SolarEnergyRacers/solar_car_control_system_v6/lib_common/CAN/CANBus.cpp

//
// CAN Bus
//
#include <Arduino.h>
#include <CANBus.h>
#include <CarState.h>
#include <Console.h>
#include <Helper.h>
#include <I2CBus.h>
#include <System.h>
#include <driver/twai.h>
#include <esp_err.h>
#include <esp_intr_alloc.h>
#include <fmt/core.h>
#include <freertos/FreeRTOS.h>
#include <freertos/semphr.h>
#include <global_definitions.h>

extern CarState carState;
extern Console console;
extern I2CBus i2cBus;
extern CANBus canBus;
extern bool SystemInited;

using namespace std;

constexpr uint16_t CANBus::MAX_RX_PACKETS_PER_CYCLE;
constexpr uint16_t CANBus::MAX_TX_PACKETS_PER_CYCLE;
constexpr uint16_t CANBus::TX_PRIORITY_SCAN_WINDOW;
constexpr uint16_t CANBus::REINIT_FAIL_THRESHOLD;
constexpr uint32_t CANBus::REINIT_COOLDOWN_MS;

static inline bool is_relevant_can_id(uint16_t packetId) {
    if (packetId == (AC_BASE_ADDR | 0x00) ||
        packetId == (DC_BASE_ADDR | 0x00) || packetId == (DC_BASE_ADDR | 0x01)) {
        return true;
    }

    if (packetId == BMS_BASE_ADDR ||
        packetId == (BMS_BASE_ADDR | 0xF7) ||
        packetId == (BMS_BASE_ADDR | 0xF8) ||
        packetId == (BMS_BASE_ADDR | 0xF9) ||
        packetId == (BMS_BASE_ADDR | 0xFA) ||
        packetId == (BMS_BASE_ADDR | 0xFD)) {
        return true;
    }

    if (packetId == (MPPT1_BASE_ADDR | 0x01) || packetId == (MPPT1_BASE_ADDR | 0x02) ||
        packetId == (MPPT2_BASE_ADDR | 0x01) || packetId == (MPPT2_BASE_ADDR | 0x02) ||
        packetId == (MPPT3_BASE_ADDR | 0x01) || packetId == (MPPT3_BASE_ADDR | 0x02) ||
        packetId == (MPPT4_BASE_ADDR | 0x01) || packetId == (MPPT4_BASE_ADDR | 0x02)) {
        return true;
    }

    return false;
}

static inline bool is_critical_can_tx_id(uint16_t packetId) {
    // Only the 0x661 packet carries a dedicated sequence byte in data byte 5.
    // The 0x650/0x660 life-sign packets use the first 16 bits as a heartbeat
    // value, so they should not trigger sequence-gap warnings.
    return packetId == (DC_BASE_ADDR | 0x01);
}

static bool extract_critical_sequence(uint16_t packetId, CANPacket& packet,
                                      uint16_t& sequence, uint8_t& bitWidth) {
    switch (packetId) {
        case (DC_BASE_ADDR | 0x01):
            sequence = packet.getData_u8(5);
            bitWidth = 8;
            return true;
        default:
            return false;
    }
}

static bool read_can_packet(CANPacket& outPacket) {
    twai_message_t message = {};
    esp_err_t err = twai_receive(&message, 0);
    if (err != ESP_OK) {
        return false;
    }

    if (message.extd || message.rtr || message.data_length_code > 8) {
        return false;
    }

    uint16_t packetId = static_cast<uint16_t>(message.identifier & 0x7FF);

    if (canBus.verboseModeCanAddr) {
        string indent = "";
        if ((packetId & 0xFF0) == 0x500) indent = "";
        if ((packetId & 0xFF0) == 0x600) indent = "      ";
        if ((packetId & 0xFF0) == 0x610) indent = "            ";
        if ((packetId & 0xFF0) == 0x620) indent = "                  ";
        if ((packetId & 0xFF0) == 0x630) indent = "                        ";
        if ((packetId & 0xFF0) == 0x650) indent = "                              ";
        if ((packetId & 0xFF0) == 0x660) indent = "                                    ";
        if ((packetId & 0xF00) == 0x700) indent = "                                          ";
        console << fmt::format("CAN packet ID:{}0x{:03X}", indent, packetId) << NL;
    }
    if (!is_relevant_can_id(packetId)) {
        return false;
    }

    uint64_t rxData = 0UL;
    for (uint8_t i = 0; i < message.data_length_code; i++) {
        rxData |= (static_cast<uint64_t>(message.data[i]) << (i * 8));
    }

    outPacket = CANPacket(packetId, rxData);
    return true;
}

bool CANBus::isPacketToRenew(uint16_t packetId) {
    auto maxAgeIt = max_ages.find(packetId);
    if (maxAgeIt == max_ages.end()) {
        return false;
    }

    int32_t maxAge = maxAgeIt->second;
    if (maxAge == -1) {
        return false;
    }
    if (maxAge == 0) {
        return true;
    }

    auto ageIt = ages.find(packetId);
    if (ageIt == ages.end() || ageIt->second == INT32_MAX) {
        return true;
    }

    return millis() - ageIt->second > maxAge;
}

void CANBus::setPacketTimeStamp(uint16_t packetId, int32_t millis) {
    auto ageIt = ages.find(packetId);
    if (ageIt != ages.end()) {
        ageIt->second = millis;
    }
}

CANBus::CANBus() { init_ages(); }

string CANBus::re_init() {
    lastReinitMs = millis();
    twai_stop();
    twai_driver_uninstall();
    vTaskDelay(50 / portTICK_PERIOD_MS);
    while (rxBufferOutCritical != nullptr && rxBufferOutCritical->isAvailable()) {
        rxBufferOutCritical->pop();
    }
    while (rxBufferOut.isAvailable()) {
        rxBufferOut.pop();
    }
    while (rxBufferIn.isAvailable()) {
        rxBufferIn.pop();
    }
    return CANBus::init();
}

string CANBus::init() {
    bool hasError = false;
    counterI = 0;
    counterR = 0;
    counterW = 0;
    counterI_notAvail = 0;
    counterR_notAvail = 0;
    counterW_notAvail = 0;
    counterRxOverwrite = 0;
    counterTxOverwrite = 0;
    counterCriticalTxDrop = 0;
    counterCriticalTxFail = 0;
    counterCriticalStale = 0;
    counterCriticalSeqGap = 0;
    criticalTxRetries.clear();
    criticalStaleActive.clear();
    criticalLastSeq.clear();
    criticalSeqSeen.clear();
    txFailStreak = 0;

    counterMaxPacketsIn = 0;
    counterMaxPacketsOut = 0;

    mutex_out = xSemaphoreCreateBinary();
    xSemaphoreGive(mutex_out);

    if (rxBufferOutCritical == nullptr) {
        rxBufferOutCritical = new CANRxBuffer();
    }
    if (rxBufferOutCritical == nullptr) {
        hasError = true;
        console << "     ERROR: Critical CAN queue allocation failed. Falling back to shared TX queue.\n";
    }

    twai_general_config_t g_config = TWAI_GENERAL_CONFIG_DEFAULT(
        static_cast<gpio_num_t>(CAN_TX), static_cast<gpio_num_t>(CAN_RX), TWAI_MODE_NORMAL);
    g_config.tx_queue_len = 64;
    g_config.rx_queue_len = 64;
    // Use a shared low/medium priority interrupt to reduce allocation failures
    // on systems with many peripherals already reserving dedicated interrupt lines.
    g_config.intr_flags = ESP_INTR_FLAG_LOWMED | ESP_INTR_FLAG_SHARED;
    g_config.alerts_enabled = TWAI_ALERT_TX_FAILED | TWAI_ALERT_BUS_OFF |
                              TWAI_ALERT_BUS_RECOVERED | TWAI_ALERT_ERR_PASS;

    twai_timing_config_t t_config = TWAI_TIMING_CONFIG_125KBITS();
    twai_filter_config_t f_config = TWAI_FILTER_CONFIG_ACCEPT_ALL();

    esp_err_t installErr = twai_driver_install(&g_config, &t_config, &f_config);
    esp_err_t startErr = installErr == ESP_OK ? twai_start() : installErr;

    if (installErr != ESP_OK || startErr != ESP_OK) {
        hasError = true;
        console << fmt::format(
            "     ERROR: TWAI init failed with rx={}, tx={}, speed={} (install={}, start={}).\n",
            CAN_RX, CAN_TX, CAN_SPEED, static_cast<int>(installErr), static_cast<int>(startErr));
    } else {
        console << fmt::format("     TWAI with rx={}, tx={}, speed={} inited.\n",
                               CAN_RX, CAN_TX, CAN_SPEED);
    }
    return fmt::format("[{}] CANBus initialized.", hasError ? "--" : "ok");
}

void CANBus::exit() {
    twai_stop();
    twai_driver_uninstall();
}

void CANBus::init_ages() {
    max_ages[AC_BASE_ADDR | 0x00] = CRITICAL_CAN_STALE_TIMEOUT_MS;
    max_ages[DC_BASE_ADDR | 0x00] = CRITICAL_CAN_STALE_TIMEOUT_MS;
    max_ages[DC_BASE_ADDR | 0x01] = CRITICAL_CAN_STALE_TIMEOUT_MS;

    // init max ages
    max_ages[BMS_BASE_ADDR] = MAXAGE_BMU_HEARTBEAT;
    max_ages[BMS_BASE_ADDR | 0x1] = MAXAGE_CMU_TEMP;      // CMU1
    max_ages[BMS_BASE_ADDR | 0x2] = MAXAGE_CMU_VOLTAGES;  // CMU1
    max_ages[BMS_BASE_ADDR | 0x3] = MAXAGE_CMU_VOLTAGES;  // CMU1
    max_ages[BMS_BASE_ADDR | 0x4] = MAXAGE_CMU_TEMP;      // CMU2
    max_ages[BMS_BASE_ADDR | 0x5] = MAXAGE_CMU_VOLTAGES;  // CMU2
    max_ages[BMS_BASE_ADDR | 0x6] = MAXAGE_CMU_VOLTAGES;  // CMU2
    max_ages[BMS_BASE_ADDR | 0x7] = MAXAGE_CMU_TEMP;      // CMU3
    max_ages[BMS_BASE_ADDR | 0x8] = MAXAGE_CMU_VOLTAGES;  // CMU3
    max_ages[BMS_BASE_ADDR | 0x9] = MAXAGE_CMU_VOLTAGES;  // CMU3
    max_ages[BMS_BASE_ADDR | 0xF4] = MAXAGE_PACK_SOC;
    max_ages[BMS_BASE_ADDR | 0xF5] = MAXAGE_BALANCE_SOC;
    max_ages[BMS_BASE_ADDR | 0xF6] = MAXAGE_CHARGER_CONTROL;
    max_ages[BMS_BASE_ADDR | 0xF7] = MAXAGE_PRECHARGE_STATUS;
    max_ages[BMS_BASE_ADDR | 0xF8] = MAXAGE_MIN_MAX_U_CELL;
    max_ages[BMS_BASE_ADDR | 0xF9] = MAXAGE_MIN_MAX_T_CELL;
    max_ages[BMS_BASE_ADDR | 0xFA] = MAXAGE_PACK_VOLTAGE;
    max_ages[BMS_BASE_ADDR | 0xFB] = MAXAGE_PACK_STATUS;
    max_ages[BMS_BASE_ADDR | 0xFC] = MAXAGE_PACK_FAN_STATUS;
    max_ages[BMS_BASE_ADDR | 0xFD] = MAXAGE_EXT_PACK_STATUS;

    max_ages[MPPT1_BASE_ADDR] = MAXAGE_MPPT_INPUT;
    max_ages[MPPT1_BASE_ADDR | 0x1] = MAXAGE_MPPT_OUTPUT;
    max_ages[MPPT1_BASE_ADDR | 0x2] = MAXAGE_MPPT_TEMP;
    max_ages[MPPT1_BASE_ADDR | 0x3] = MAXAGE_MPPT_AUX_POWER;
    max_ages[MPPT1_BASE_ADDR | 0x4] = MAXAGE_MPPT_LIMITS;
    max_ages[MPPT1_BASE_ADDR | 0x5] = MAXAGE_MPPT_STATUS;
    max_ages[MPPT1_BASE_ADDR | 0x6] = MAXAGE_MPPT_POWER_CONN;

    max_ages[MPPT2_BASE_ADDR] = MAXAGE_MPPT_INPUT;
    max_ages[MPPT2_BASE_ADDR | 0x1] = MAXAGE_MPPT_OUTPUT;
    max_ages[MPPT2_BASE_ADDR | 0x2] = MAXAGE_MPPT_TEMP;
    max_ages[MPPT2_BASE_ADDR | 0x3] = MAXAGE_MPPT_AUX_POWER;
    max_ages[MPPT2_BASE_ADDR | 0x4] = MAXAGE_MPPT_LIMITS;
    max_ages[MPPT2_BASE_ADDR | 0x5] = MAXAGE_MPPT_STATUS;
    max_ages[MPPT2_BASE_ADDR | 0x6] = MAXAGE_MPPT_POWER_CONN;

    max_ages[MPPT3_BASE_ADDR] = MAXAGE_MPPT_INPUT;
    max_ages[MPPT3_BASE_ADDR | 0x1] = MAXAGE_MPPT_OUTPUT;
    max_ages[MPPT3_BASE_ADDR | 0x2] = MAXAGE_MPPT_TEMP;
    max_ages[MPPT3_BASE_ADDR | 0x3] = MAXAGE_MPPT_AUX_POWER;
    max_ages[MPPT3_BASE_ADDR | 0x4] = MAXAGE_MPPT_LIMITS;
    max_ages[MPPT3_BASE_ADDR | 0x5] = MAXAGE_MPPT_STATUS;
    max_ages[MPPT3_BASE_ADDR | 0x6] = MAXAGE_MPPT_POWER_CONN;

    max_ages[MPPT4_BASE_ADDR] = MAXAGE_MPPT_INPUT;
    max_ages[MPPT4_BASE_ADDR | 0x1] = MAXAGE_MPPT_OUTPUT;
    max_ages[MPPT4_BASE_ADDR | 0x2] = MAXAGE_MPPT_TEMP;
    max_ages[MPPT4_BASE_ADDR | 0x3] = MAXAGE_MPPT_AUX_POWER;
    max_ages[MPPT4_BASE_ADDR | 0x4] = MAXAGE_MPPT_LIMITS;
    max_ages[MPPT4_BASE_ADDR | 0x5] = MAXAGE_MPPT_STATUS;
    max_ages[MPPT4_BASE_ADDR | 0x6] = MAXAGE_MPPT_POWER_CONN;

    // init ages
    ages[AC_BASE_ADDR | 0x00] = INT32_MAX;
    ages[DC_BASE_ADDR | 0x00] = INT32_MAX;
    ages[DC_BASE_ADDR | 0x01] = INT32_MAX;

    ages[BMS_BASE_ADDR] = INT32_MAX;
    ages[BMS_BASE_ADDR | 0x1] = INT32_MAX;  // CMU1
    ages[BMS_BASE_ADDR | 0x2] = INT32_MAX;  // CMU1
    ages[BMS_BASE_ADDR | 0x3] = INT32_MAX;  // CMU1
    ages[BMS_BASE_ADDR | 0x4] = INT32_MAX;  // CMU2
    ages[BMS_BASE_ADDR | 0x5] = INT32_MAX;  // CMU2
    ages[BMS_BASE_ADDR | 0x6] = INT32_MAX;  // CMU2
    ages[BMS_BASE_ADDR | 0x7] = INT32_MAX;  // CMU3
    ages[BMS_BASE_ADDR | 0x8] = INT32_MAX;  // CMU3
    ages[BMS_BASE_ADDR | 0x9] = INT32_MAX;  // CMU3
    ages[BMS_BASE_ADDR | 0xF4] = INT32_MAX;
    ages[BMS_BASE_ADDR | 0xF5] = INT32_MAX;
    ages[BMS_BASE_ADDR | 0xF6] = INT32_MAX;
    ages[BMS_BASE_ADDR | 0xF7] = INT32_MAX;
    ages[BMS_BASE_ADDR | 0xF8] = INT32_MAX;
    ages[BMS_BASE_ADDR | 0xF9] = INT32_MAX;
    ages[BMS_BASE_ADDR | 0xFA] = INT32_MAX;
    ages[BMS_BASE_ADDR | 0xFB] = INT32_MAX;
    ages[BMS_BASE_ADDR | 0xFC] = INT32_MAX;
    ages[BMS_BASE_ADDR | 0xFD] = INT32_MAX;

    ages[MPPT1_BASE_ADDR] = INT32_MAX;
    ages[MPPT1_BASE_ADDR | 0x1] = INT32_MAX;
    ages[MPPT1_BASE_ADDR | 0x2] = INT32_MAX;
    ages[MPPT1_BASE_ADDR | 0x3] = INT32_MAX;
    ages[MPPT1_BASE_ADDR | 0x4] = INT32_MAX;
    ages[MPPT1_BASE_ADDR | 0x5] = INT32_MAX;
    ages[MPPT1_BASE_ADDR | 0x6] = INT32_MAX;

    ages[MPPT2_BASE_ADDR] = INT32_MAX;
    ages[MPPT2_BASE_ADDR | 0x1] = INT32_MAX;
    ages[MPPT2_BASE_ADDR | 0x2] = INT32_MAX;
    ages[MPPT2_BASE_ADDR | 0x3] = INT32_MAX;
    ages[MPPT2_BASE_ADDR | 0x4] = INT32_MAX;
    ages[MPPT2_BASE_ADDR | 0x5] = INT32_MAX;
    ages[MPPT2_BASE_ADDR | 0x6] = INT32_MAX;

    ages[MPPT3_BASE_ADDR] = INT32_MAX;
    ages[MPPT3_BASE_ADDR | 0x1] = INT32_MAX;
    ages[MPPT3_BASE_ADDR | 0x2] = INT32_MAX;
    ages[MPPT3_BASE_ADDR | 0x3] = INT32_MAX;
    ages[MPPT3_BASE_ADDR | 0x4] = INT32_MAX;
    ages[MPPT3_BASE_ADDR | 0x5] = INT32_MAX;
    ages[MPPT3_BASE_ADDR | 0x6] = INT32_MAX;

    ages[MPPT4_BASE_ADDR] = INT32_MAX;
    ages[MPPT4_BASE_ADDR | 0x1] = INT32_MAX;
    ages[MPPT4_BASE_ADDR | 0x2] = INT32_MAX;
    ages[MPPT4_BASE_ADDR | 0x3] = INT32_MAX;
    ages[MPPT4_BASE_ADDR | 0x4] = INT32_MAX;
    ages[MPPT4_BASE_ADDR | 0x5] = INT32_MAX;
    ages[MPPT4_BASE_ADDR | 0x6] = INT32_MAX;
}

CANPacket
CANBus::writePacket(uint16_t adr,
                    uint16_t data_u16_0,  // Target Speed [float as value\*1000]
                    uint16_t data_u16_1,  // Target Power [float as value\*1000]
                    int8_t data_i8_4,     // Display Acceleration
                    uint8_t data_u8_5,    // empty
                    uint8_t data_u8_6,    // Display Speed
                    bool b_56,            // Fwd [1] / Bwd [0]
                    bool b_57,            // Button Lvl Brake Pedal
                    bool b_58,            // MC Off [0] / On [1]
                    bool b_59,            // Constant Mode Off [false], On [true]
                    bool b_60,            // empty
                    bool b_61,            // empty
                    bool b_62,            // empty
                    bool b_63,            // empty
                    bool force) {
    uint64_t data = 0;
    CANPacket packet = CANPacket(adr, data);
    packet.setData_u16(0, data_u16_0);
    packet.setData_u16(1, data_u16_1);
    packet.setData_i8(4, data_i8_4);
    packet.setData_u8(5, data_u8_5);
    packet.setData_u8(6, data_u8_6);
    packet.setData_b(56, b_56);
    packet.setData_b(57, b_57);
    packet.setData_b(58, b_58);
    packet.setData_b(59, b_59);
    packet.setData_b(60, b_60);
    packet.setData_b(61, b_61);
    packet.setData_b(62, b_62);
    packet.setData_b(63, b_63);
    return writePacket(adr, packet, force);
}

CANPacket
CANBus::writePacket(uint16_t adr,
                    uint16_t data_u16_0,  // LifeSign
                    uint16_t data_u16_1,  // Potentiometer value
                    uint16_t data_u16_2,  // HAL-paddle Acceleration ADC value
                    uint16_t data_u16_3,  // HAL-paddle Deceleration ADC value
                    bool force) {
    uint64_t data = 0UL;
    CANPacket packet = CANPacket(adr, data);
    packet.setData_u16(0, data_u16_0);
    packet.setData_u16(1, data_u16_1);
    packet.setData_u16(2, data_u16_2);
    packet.setData_u16(3, data_u16_3);
    return writePacket(adr, packet, force);
}

CANPacket CANBus::writePacket(uint16_t adr,
                              uint16_t data_u16_0,  // LifeSign
                              uint8_t data_u8_2,    // Kp * 100
                              uint8_t data_u8_3,    // Ki * 100
                              uint8_t data_u8_4,    // Kd * 100
                              uint8_t data_u8_5,    // GlideMode 0...7: 0:glide, 3:half glide/half recup, 7:recuperation
                              bool data_b_48,       // ConstantMode Speed/Power
                              bool data_b_49,       // confirmDriverInfoConfirm
                              bool force) {
    uint64_t data = 0UL;
    CANPacket packet = CANPacket(adr, data);
    packet.setData_u16(0, data_u16_0);
    packet.setData_u8(2, data_u8_2);
    packet.setData_u8(3, data_u8_3);
    packet.setData_u8(4, data_u8_4);
    packet.setData_u8(5, data_u8_5);
    packet.setData_b(48, data_b_48);
    packet.setData_b(49, data_b_49);
    return writePacket(adr, packet, force);
}

std::map<uint16_t, CANPacket> packetsLast;
CANPacket CANBus::writePacket(uint16_t adr, CANPacket packet, bool force) {
    if (force || packetsLast.find(adr) == packetsLast.end() ||
        packetsLast[adr].getData_i64() != packet.getData_i64()) {
        packetsLast[adr] = packet;
        pushOut(packet);
    }
    return packet;
}

void CANBus::write_rx_packet(CANPacket packet) {
    static constexpr uint8_t CRITICAL_TX_MAX_RETRY = 3;
    static constexpr uint16_t TX_FAIL_RECOVERY_THRESHOLD = 50;

    auto retry_critical_packet = [&](uint16_t packetId) {
        if (!is_critical_control_id(packetId)) {
            return;
        }
        uint8_t& retries = criticalTxRetries[packetId];
        if (retries < CRITICAL_TX_MAX_RETRY) {
            retries++;
            pushOut(packet);
        }
    };

    uint16_t adr = 0;
    try {
        if (xSemaphoreTake(mutex_out, (TickType_t)32) != pdTRUE) {
            counterW_notAvail++;
            txFailStreak++;
            if (is_critical_control_id(packet.getId())) {
                counterCriticalTxFail++;
            }
            retry_critical_packet(packet.getId());
            if (counterW_notAvail > TX_FAIL_RECOVERY_THRESHOLD && (millis() - lastReinitMs) > (REINIT_COOLDOWN_MS / 2)) {
                twai_status_info_t statusInfo = {};
                if (twai_get_status_info(&statusInfo) == ESP_OK && statusInfo.state == TWAI_STATE_BUS_OFF) {
                    console << "WARN: TWAI bus-off detected during transmit failure, initiating recovery." << NL;
                    twai_initiate_recovery();
                } else {
                    console << "WARN: Reinitializing CAN after repeated transmit failure without bus-off." << NL;
                    re_init();
                }
            }
            return;
        }
        adr = packet.getId();
        if (adr == 0) {
            xSemaphoreGive(mutex_out);
            return;
        }

        counterW++;
        if (verboseModeCanOutNative)
            console << print_raw_packet("W", packet) << NL;

        twai_message_t message = {};
        message.identifier = adr;
        message.extd = 0;
        message.rtr = 0;
        message.data_length_code = 8;
        for (uint8_t i = 0; i < 8; i++) {
            message.data[i] = static_cast<uint8_t>(packet.getData_u8(i));
        }

        bool ok = twai_transmit(&message, pdMS_TO_TICKS(5)) == ESP_OK;
        xSemaphoreGive(mutex_out);
        if (!ok) {
            counterW_notAvail++;
            if (is_critical_control_id(adr)) {
                counterCriticalTxFail++;
            }
            retry_critical_packet(adr);
            if ((counterW_notAvail % 100) == 0) {
                console << fmt::format("CAN transmit timeout/fail (W_notAvail={})\n", counterW_notAvail);
            }
            if (counterW_notAvail > TX_FAIL_RECOVERY_THRESHOLD && (millis() - lastReinitMs) > (REINIT_COOLDOWN_MS / 2)) {
                twai_status_info_t statusInfo = {};
                if (twai_get_status_info(&statusInfo) == ESP_OK && statusInfo.state == TWAI_STATE_BUS_OFF) {
                    console << "WARN: TWAI bus-off detected during transmit error, initiating recovery." << NL;
                    twai_initiate_recovery();
                } else {
                    console << "WARN: Reinitializing CAN after repeated transmit errors without bus-off." << NL;
                    re_init();
                }
            }
        } else {
            counterW_notAvail = 0;
            txFailStreak = 0;
            if (is_critical_control_id(adr)) {
                criticalTxRetries[adr] = 0;
            }
        }
    } catch (exception& ex) {
        xSemaphoreGive(mutex_out);
        txFailStreak++;
        uint16_t packetId = adr > 0 ? adr : packet.getId();
        if (is_critical_control_id(packetId)) {
            counterCriticalTxFail++;
        }
        retry_critical_packet(packetId);
        console << "ERROR: Couldn not send uint64_t data to address " << adr
                << ", ex: " << ex.what() << NL;
    }
}

string CANBus::print_raw_packet(const string msg, CANPacket packet) {
    return fmt::format(
        "C{}-{}-[I:{:02d}|{:02d},O:{:02d}|{:02d}]={}=Id=0x{:03x}-data: {:016x} "
        "-- {:02x} - {:02x} - {:02x} - {:02x} - {:02x} - "
        "{:02x} - {:02x} - {:02x}",
        xPortGetCoreID(), esp_timer_get_time() / 1000000, availablePacketsIn(),
        getMaxPacketsBufferInUsage(), availablePacketsOut(),
        getMaxPacketsBufferOutUsage(), msg, packet.getId(), packet.getData_u64(),
        packet.getData_u8(7), packet.getData_u8(6), packet.getData_u8(5),
        packet.getData_u8(4), packet.getData_u8(3), packet.getData_u8(2),
        packet.getData_u8(1), packet.getData_u8(0));
}

void CANBus::task(void* pvParams) {
    deadCounter = 0;
    // static constexpr uint16_t MAX_RX_PACKETS_PER_CYCLE = 48;
    // static constexpr uint16_t MAX_TX_PACKETS_PER_CYCLE = 4;
    // static constexpr uint16_t TX_PRIORITY_SCAN_WINDOW = 16;
    // static constexpr uint16_t REINIT_FAIL_THRESHOLD = 200;
    // static constexpr uint32_t REINIT_COOLDOWN_MS = 8000;

    while (1) {
        report_task_stack(this);
        if (SystemInited) {
            if (deadCounter == 0) {
                deadCounter = millis() + 15e3;  // on boot: do not terminate for some time
            }
            if ((counterR_notAvail > REINIT_FAIL_THRESHOLD || counterI_notAvail > REINIT_FAIL_THRESHOLD ||
                 txFailStreak > REINIT_FAIL_THRESHOLD) &&
                (millis() - lastReinitMs > REINIT_COOLDOWN_MS)) {
                console << NL
                        << fmt::format("CANBus REINIT trigger: I{}|{}, R{}|{}, W{}|{}, txFailStreak={}, rxOv={}, txOv={}, critTxDrop={}, critTxFail={}, critStale={}, critSeqGap={}, qCrit={}, qTel={}",
                                       counterI_notAvail, counterI, counterR_notAvail,
                                       counterR, counterW_notAvail, counterW, txFailStreak,
                                       counterRxOverwrite, counterTxOverwrite,
                                       counterCriticalTxDrop, counterCriticalTxFail,
                                       counterCriticalStale, counterCriticalSeqGap,
                                       availablePacketsOutCritical(), availablePacketsOutTelemetry())
                        << NL;
                canBus.re_init();
            }

            // if(verboseModeCanOutNative) console << "CAN 1" << NL;

            uint16_t rxIngested = 0;
            while (rxIngested < MAX_RX_PACKETS_PER_CYCLE) {
                CANPacket packet;
                if (!read_can_packet(packet)) {
                    break;
                }
                canBus.pushIn(packet);
                canBus.counterI++;
                canBus.counterI_notAvail = 0;
                rxIngested++;
            }

            uint16_t rxProcessed = 0;
            while (rxBufferIn.isAvailable() && rxProcessed < MAX_RX_PACKETS_PER_CYCLE) {
                CANPacket packet = rxBufferIn.pop();
                uint16_t packetId = packet.getId();
                if (packetId == 0 || is_to_ignore_packet(packetId)) {
                    rxProcessed++;
                    continue;
                }

                setPacketTimeStamp(packetId, millis());

                if (is_critical_can_tx_id(packetId)) {
                    uint16_t sequence = 0;
                    uint8_t bitWidth = 0;
                    if (extract_critical_sequence(packetId, packet, sequence, bitWidth)) {
                        if (criticalSeqSeen[packetId]) {
                            uint16_t prev = criticalLastSeq[packetId];
                            uint16_t delta = 0;
                            if (bitWidth == 8) {
                                delta = static_cast<uint8_t>(sequence) - static_cast<uint8_t>(prev);
                                if (delta > 1 && delta < 128) {
                                    counterCriticalSeqGap += (delta - 1);
                                    console << fmt::format(
                                        "WARN: Critical CAN sequence gap on 0x{:03x}, missed {} packet(s).\n",
                                        packetId, delta - 1);
                                }
                            } else {
                                delta = static_cast<uint16_t>(sequence - prev);
                                if (delta > 1 && delta < 0x8000) {
                                    counterCriticalSeqGap += (delta - 1);
                                    console << fmt::format(
                                        "WARN: Critical CAN sequence gap on 0x{:03x}, missed {} packet(s).\n",
                                        packetId, delta - 1);
                                }
                            }
                        }
                        criticalLastSeq[packetId] = sequence;
                        criticalSeqSeen[packetId] = true;
                    }
                }

                handle_rx_packet(packet);
                deadCounter = millis();
                rxProcessed++;
                if ((rxProcessed % 16) == 0) {
                    vTaskDelay(1);
                }
            }

            uint32_t now = millis();
            const uint16_t criticalIds[] = {
                static_cast<uint16_t>(AC_BASE_ADDR | 0x00),
                static_cast<uint16_t>(DC_BASE_ADDR | 0x00),
                static_cast<uint16_t>(DC_BASE_ADDR | 0x01)};

            for (uint16_t packetId : criticalIds) {
                bool stale = false;
                auto ageIt = ages.find(packetId);
                if (ageIt != ages.end() && ageIt->second != INT32_MAX) {
                    stale = (now - static_cast<uint32_t>(ageIt->second)) >
                            static_cast<uint32_t>(CRITICAL_CAN_STALE_TIMEOUT_MS);
                }

                bool wasStale = criticalStaleActive[packetId];
                if (stale && !wasStale) {
                    criticalStaleActive[packetId] = true;
                    counterCriticalStale++;
                    console << fmt::format(
                        "WARN: Critical CAN packet 0x{:03x} stale for >{}ms.\n",
                        packetId, CRITICAL_CAN_STALE_TIMEOUT_MS);
                } else if (!stale && wasStale) {
                    criticalStaleActive[packetId] = false;
                    console << fmt::format(
                        "INFO: Critical CAN packet 0x{:03x} recovered.\n", packetId);
                }
            }

            // if(verboseModeCanOutNative) console << "CAN 2" << NL;

            // uint bench = esp_timer_get_time(); // this might be an unacceptably long time to disable all and any context switches / ISR? -> log time (~80us -> ok?)
            if (counterW_notAvail > 40 && availablePacketsOutTelemetry() > 8) {
                while (rxBufferOut.isAvailable() && availablePacketsOutTelemetry() > 4) {
                    uint16_t scanCount = min((uint16_t)availablePacketsOutTelemetry(), TX_PRIORITY_SCAN_WINDOW);
                    CANPacket scanBuffer[TX_PRIORITY_SCAN_WINDOW];
                    for (uint16_t i = 0; i < scanCount; i++) {
                        scanBuffer[i] = rxBufferOut.pop();
                        if (i != 0) {
                            rxBufferOut.push(scanBuffer[i]);
                        }
                    }
                }
            }

            uint16_t txProcessed = 0;
            while (rxBufferOutCritical != nullptr && rxBufferOutCritical->isAvailable() &&
                   txProcessed < MAX_TX_PACKETS_PER_CYCLE) {
                write_rx_packet(rxBufferOutCritical->pop());
                txProcessed++;
            }

            while (rxBufferOut.isAvailable() && txProcessed < MAX_TX_PACKETS_PER_CYCLE) {
                write_rx_packet(rxBufferOut.pop());
                txProcessed++;
                if ((txProcessed % 8) == 0) {
                    vTaskDelay(1);
                }
            }

            // if(verboseModeCanOutNative) console << "CAN 3: " << (uint)(esp_timer_get_time() - bench) << NL;

            // if (millis() > deadCounter + 2e3) {
            //   console << "CAN presumed dead. Rebooting..." << NL;
            //   ESP.restart();
            // }
            twai_status_info_t statusInfo = {};
            if (twai_get_status_info(&statusInfo) == ESP_OK &&
                statusInfo.state == TWAI_STATE_BUS_OFF) {
                console << "WARN: TWAI bus-off detected, initiating recovery.\n";
                twai_initiate_recovery();
            }
        }
        taskSuspend();
    }
}
