SolarEnergyRacers/solar_car_control_system_v6/lib_common/CAN/CANPacket.h

#ifndef SOLAR_CAR_CONTROL_SYSTEM_CANPACKET_H
#define SOLAR_CAR_CONTROL_SYSTEM_CANPACKET_H

#include <Arduino.h>

using namespace std;

// ┌───────────────────┬───────────────────────────────────────────────────────────────┐
// │ 64-bit partition  │                              [0]                              │
// │ (u64, i64)        ├───────────────────────────────────────────────────────────────┤
// │              bit  │63                            ···                             0│
// ├───────────────────┼───────────────────────────────┬───────────────────────────────┤
// │ 32-bit partition  │            [1]                │            [0]                │
// │ (u32, i32, f32)   ├───────────────────────────────┼───────────────────────────────┤
// │              bit  │63         ...               32│31                         ...0│
// ├───────────────────┼───────────────┬───────────────┼───────────────┬───────────────┤
// │ 16-bit partition  │      W3       │      W2       │      W1       │      W0       │
// │ (u16, i16)        ├───────────────┼───────────────┼───────────────┼───────────────┤
// │              bit  │63    ...    48│47    ...    32│31    ...    16│15    ...     0│
// ├───────────────────┼───────┬───────┼───────┬───────┼───────┬───────┼───────┬───────┤
// │ 8-bit partition   │  B7   │  B6   │  B5   │  B4   │  B3   │  B2   │  B1   │  B0   │
// │ (u8, i8)          ├───────┼───────┼───────┼───────┼───────┼───────┼───────┼───────┤
// │              bit  │63...56│55...48│47...40│39...32│31...24│23...16│15... 8│7 ... 0│
// ├───────────────────┼───────┴───────┴───────┴───────┴───────┴───────┴───────┴───────┤
// │ 1-bit partition   │b63                      ...                                 b0│
// │ (b64 as uint64_t) ├───────────────────────────────────────────────────────────────┤
// │              bit  │63                       ···                                  0│
// └───────────────────┴───────────────────────────────────────────────────────────────┘
//                      MSB  ◄───────────────────────────────────────────────────►  LSB
//

typedef union {
  uint64_t b64;
  uint8_t data_u8[8];
  int8_t data_i8[8];
  uint16_t data_u16[4];
  int16_t data_i16[4];
  uint32_t data_u32[2];
  int32_t data_i32[2];
  float data_f32[2];
  uint64_t data_u64;
  int64_t data_i64;
} group_64;

class CANPacket {
private:
  uint16_t id;
  group_64 data;

public:
  CANPacket();
  CANPacket(uint16_t id, uint8_t data[]);
  CANPacket(uint16_t id, uint64_t data);

  CANPacket &operator=(const CANPacket &that) {
    if (this != &that) {
      this->id = that.id;
      this->data = that.data;
    }

    return *this;
  };

  void setId(uint16_t id);
  uint16_t getId();

  void setData(uint8_t data[]);
  void setData(uint64_t data) { this->data.data_u64 = data; };

  void setData_u64(uint8_t index, uint64_t value) { this->data.data_u64 = value; }
  uint64_t getData_u64() { return this->data.data_u64; }
  void setData_i64(uint8_t index, int64_t value) { this->data.data_i64 = value; }
  int64_t getData_i64() { return this->data.data_i64; }

  void setData_u32(uint8_t index, uint32_t value) { this->data.data_u32[index] = value; }
  uint32_t getData_u32(uint8_t index) { return this->data.data_u32[index]; }
  void setData_i32(uint8_t index, int32_t value) { this->data.data_i32[index] = value; }
  int32_t getData_i32(uint8_t index) { return this->data.data_i32[index]; }
  void setData_f32(uint8_t index, float value) { this->data.data_f32[index] = value; }
  float getData_f32(uint8_t index) { return this->data.data_f32[index]; }

  void setData_u16(uint8_t index, uint16_t value) { this->data.data_u16[index] = value; }
  uint16_t getData_u16(uint8_t index) { return this->data.data_u16[index]; }
  void setData_i16(uint8_t index, int16_t value) { this->data.data_i16[index] = value; }
  int16_t getData_i16(uint8_t index) { return this->data.data_i16[index]; }

  void setData_u8(uint8_t index, uint8_t value) { this->data.data_u8[index] = value; }
  uint8_t getData_u8(uint8_t index) { return this->data.data_u8[index]; }
  void setData_i8(uint8_t index, int8_t value) { this->data.data_i8[index] = value; }
  int8_t getData_i8(uint8_t index) { return this->data.data_i8[index]; }

  void setData_b(uint8_t index, bool value) {
    if (value) {
      this->data.b64 |= BIT64(index);
    } else {
      this->data.b64 &= ~BIT64(index);
    }
  }
  bool getData_b(uint8_t index) { return this->data.b64 & BIT64(index); }

  static const uint BUFFER_SIZE = 11;
  void to_serial(uint16_t adr, std::array<uint8_t, BUFFER_SIZE> &buffer);
};

// if (status & BIT(1)) {
//    // Do something if bit 1 is set
// } elseif (~status | BIT(2) {
//    // Do something else if bit 2 is cleared
// } else  {
//    // Set bits 1 and 2
//    status |= BIT(1) | BIT(2)
//    // Clear bits 0 and 4
//    status &= ~(BIT(0) | BIT(4))
//    // Toggle bit 5
//    status ^= BIT(5)
// }

#endif // SOLAR_CAR_CONTROL_SYSTEM_CANPACKET_H
